luk6xff/usbmux/app/src/commander.h

#pragma once

#include <Arduino.h>

#include <vector>

#include "usbmuxdriver.h"
#include "power-relay.h"


///< Forward declaration of Actual Command classes
class CommandMsg;
class CmdSetChannelMsg;
class CmdSetRelayMsg;
class CmdSetWifiConfigMsg;
class CmdDeviceInfoMsg;
class CmdDeviceResetMsg;


/**
 * @brief Command Handler class.
 */
class CmdHandler
{
public:
    explicit CmdHandler();
    void handle(CmdSetChannelMsg& msg);
    void handle(CmdSetRelayMsg& msg);
    void handle(CmdSetWifiConfigMsg& msg);
    void handle(CmdDeviceInfoMsg& msg);
    void handle(CmdDeviceResetMsg& msg);
    void handle(CommandMsg& msg);

private:
    UsbMuxDriver m_usbMux;
    PowerRelay m_pwrRelay;
};


/**
 * @brief Command message interface class.
 */
class CommandMsg
{

public:
    void dispatch(CmdHandler& handler)
    {
        dispatchImpl(handler);
    }

protected:
    virtual void dispatchImpl(CmdHandler& handler) = 0; 
};


/**
 * @brief Command message base class.
 * @see https://en.wikibooks.org/wiki/More_C%2B%2B_Idioms/Curiously_Recurring_Template_Pattern
 */
template <typename TDerived>
class CommandMsgBase : public CommandMsg
{

protected:

    virtual void dispatchImpl(CmdHandler& handler) override
    {
        handler.handle(static_cast<TDerived&>(*this));
    }

};


////////////////////////////////////////////////////////////////////////////////
///< Actual Command classes
////////////////////////////////////////////////////////////////////////////////

//------------------------------------------------------------------------------
class CmdSetChannelMsg : public CommandMsgBase<CmdSetChannelMsg>
{

public:
    CmdSetChannelMsg(UsbMuxDriver::UsbChannelNumber chNum=UsbMuxDriver::UsbChannelNumber::USB_CHANNEL_INVALID,
                     UsbMuxDriver::UsbIdState idState=UsbMuxDriver::UsbIdState::USB_ID_HIGH,
                     bool disable=false)
        : channelNumber(chNum)
        , usbIdState(idState)
        , disableChannels(disable)
    {
    }

public:
    UsbMuxDriver::UsbChannelNumber channelNumber;
    UsbMuxDriver::UsbIdState usbIdState;
    bool disableChannels;
};


//------------------------------------------------------------------------------
class CmdSetRelayMsg : public CommandMsgBase<CmdSetRelayMsg>
{

public:
    CmdSetRelayMsg()
        : relayState(PowerRelay::RelayState::RELAY_OFF)
        , reset(false)
        , resetTimeoutMs(k_defaultTimeoutMs)
    {
    }

    CmdSetRelayMsg (PowerRelay::RelayState state, bool reset=false, uint32_t resetTime=k_defaultTimeoutMs)
        : relayState(state)
        , reset(reset)
        , resetTimeoutMs(resetTime)
    {
    }

public:
    PowerRelay::RelayState relayState;
    bool reset;
    uint32_t resetTimeoutMs;

    static int const k_defaultTimeoutMs = 1000;
};


//------------------------------------------------------------------------------
class CmdSetWifiConfigMsg : public CommandMsgBase<CmdSetWifiConfigMsg>
{
public:
    CmdSetWifiConfigMsg(uint8_t id=0, String ssid="", String pass="",
                        bool read=false, bool reconnect=false)
    : wifiId(id)
    , wifiSsid(ssid)
    , wifiPass(pass)
    , wifiRead(read)
    , wifiReconnect(reconnect)
    {
    }

public:
    uint8_t wifiId;
    String wifiSsid;
    String wifiPass;
    bool wifiRead;
    bool wifiReconnect;
};


//------------------------------------------------------------------------------
class CmdDeviceInfoMsg : public CommandMsgBase<CmdDeviceInfoMsg>
{
public:
    CmdDeviceInfoMsg() = default;
};


//------------------------------------------------------------------------------
class CmdDeviceResetMsg : public CommandMsgBase<CmdDeviceResetMsg>
{
public:
    CmdDeviceResetMsg() = default;
};



//------------------------------------------------------------------------------
/**
 * @brief A place where all the device commands are being dispatched and run :)
 */
class Commander
{

public:

    /**
     * @brief Ctor
     */
    explicit Commander();

    void processCmdMsg(CommandMsg& msg);

private:


private:
    CmdHandler m_cmdHandler;
};
