luk6xff/usbmux/app/src/device-info.h

#pragma once

#include <Arduino.h>

template<typename T>
struct InfoValue
{
    InfoValue(const char *name, T value, const char *unit="", const char *icon="glyphicon-scale")
        : m_name(name)
        , m_value(String(value))
        , m_unit(unit)
        , m_glyphIcon(icon)
    {
    }

    String toServerJson()
    {
        String json = "{\"name\":\""+ m_name + "\",\"value\":\"" + m_value + "\",\"unit\":\"" + m_unit + "\",\"glyph\":\"" + m_glyphIcon + "\"}";
        return json;
    }

    String toValueString()
    {
        String val = m_name + ": " + m_value + " " + m_unit;
        return val;
    }

public:
    const String &name()
    {
        return m_name;
    }

    const String &val()
    {
        return m_value;
    }

    const String &unit()
    {
        return m_unit;
    }

    const String &icon()
    {
        return m_glyphIcon;
    }

private:
    String m_name;
    String m_value;
    String m_unit;
    String m_glyphIcon;
};



class DeviceInfo
{

public:
    explicit DeviceInfo();

    String latest();
    String createDevInfoTable();
    String createDynamicDevInfo();

private:
    InfoValue<String> buildAuthor;
    InfoValue<String> buildDate;
    InfoValue<String> buildTime;
    InfoValue<uint16_t> vcc;
    InfoValue<uint32_t> chipId;
    InfoValue<String> fullVersion;
    InfoValue<uint32_t> bootVersion;
    InfoValue<uint32_t> cpuFreqMhz;
    InfoValue<String> resetInfo;
    InfoValue<uint32_t> flashChipRealSize;
    InfoValue<uint32_t> appSize;
    InfoValue<uint32_t> freeHeap;
    InfoValue<uint32_t> freeStack;
};
