luk6xff/usbmux/app/src/utils.cpp

#include "utils.h"
#include "timerManager.h"


#define DBG_BAUDRATE 115200
#define DBG_VERBOSITY_LEVEL DBG_INFO

//------------------------------------------------------------------------------
void utils::init()
{
    Serial.begin(DBG_BAUDRATE);
    Debug.setDebugOutputStream(&Serial);
    Debug.setDebugLevel(DBG_VERBOSITY_LEVEL);
    Debug.timestampOff();
    inf(">>> USBMUX by luk6xff 2020 <<<\r\n");
}

//------------------------------------------------------------------------------
void utils::update()
{
    //Update all the timers at once
    TimerManager::instance().update();
}
