luk6xff/usbmux/app/src/utils.h

#pragma once

#include "DebugUtils.h"

namespace utils
{
    /**
     * @brief Initializes, Serial and debug verbisty
     * @note Must be called in the main.cpp in the setup function
     */
    void init();

    /**
     * @brief Updates all the needed global utils state
     * @note Must be called in the main.cpp in the loop function
     */
    void update();

    #define dbg(fmt, ...) \
        do { \
            Debug.print(DBG_VERBOSE, fmt,  ##__VA_ARGS__); \
        } while(0)

    #define inf(fmt, ...) \
        do { \
            Debug.print(DBG_INFO, fmt,  ##__VA_ARGS__); \
        } while(0)

    #define wrn(fmt, ...) \
        do { \
            Debug.print(DBG_WARNING, fmt,  ##__VA_ARGS__); \
        } while(0)

    #define err(fmt, ...) \
        do { \
            Debug.print(DBG_ERROR, fmt,  ##__VA_ARGS__); \
        } while(0)
};
